Tengyez/gyrogotchi/docs/model_pictures/back open.png

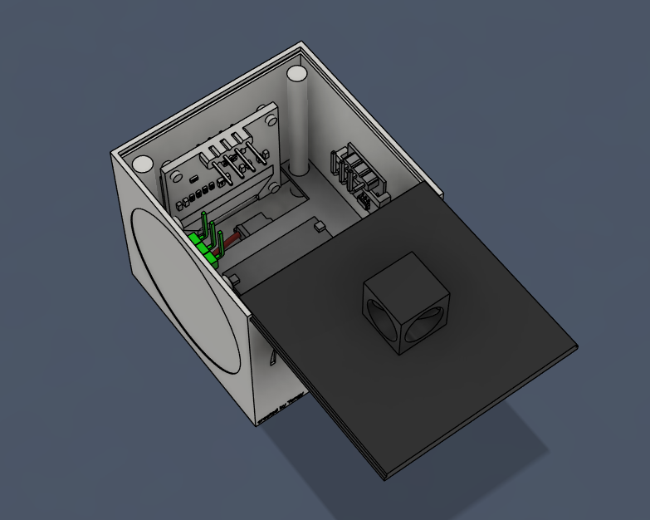
docs/model_pictures/back open.png
