Tengyez/gyrogotchi/docs/model_pictures/open.png

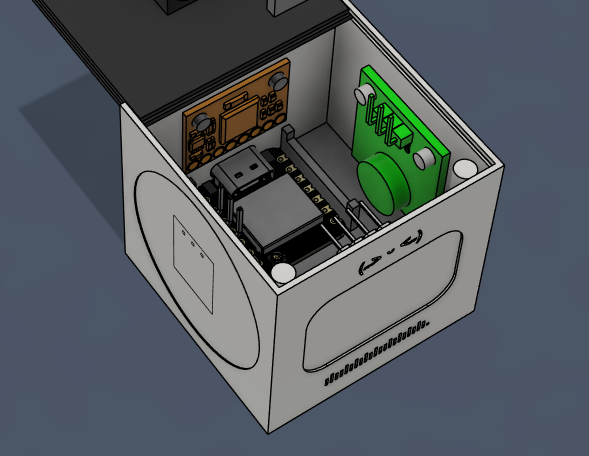
docs/model_pictures/open.png
