Tengyez/gyrogotchi/docs/model_pictures/rendered front closed.PNG

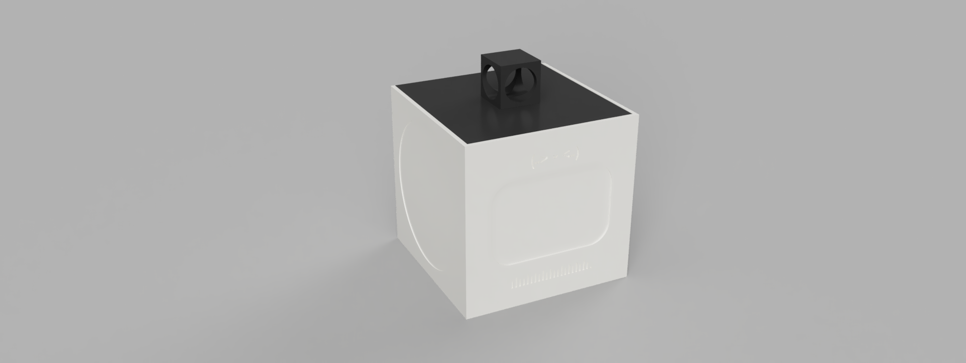
docs/model_pictures/rendered front closed.PNG
