Tengyez/gyrogotchi/docs/model_pictures/rendered front mini open.png

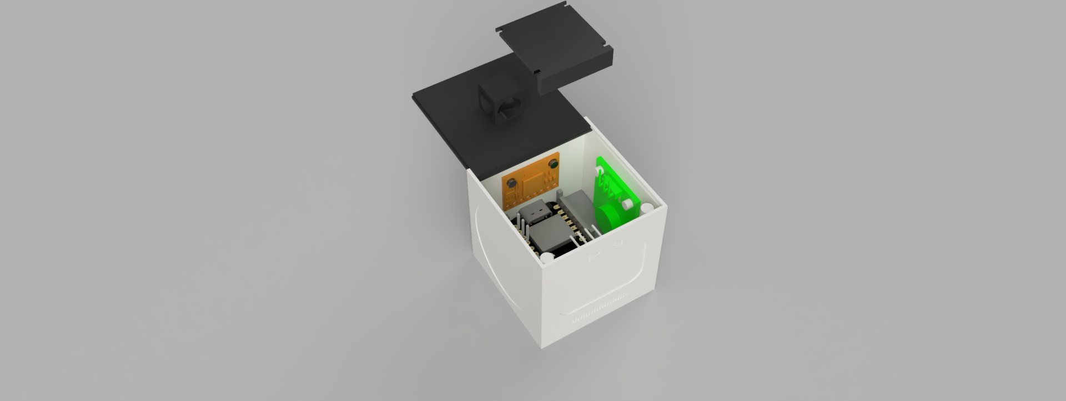
docs/model_pictures/rendered front mini open.png
