Tengyez/gyrogotchi/docs/ui.png

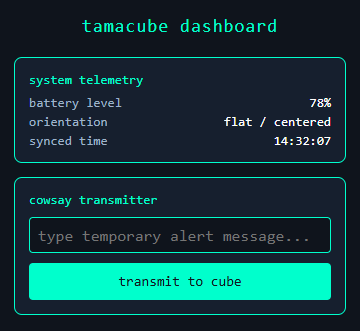
docs/ui.png
